zharfanw/fsaeuiicar/Gambar/messageImage_1562059117821.jpg

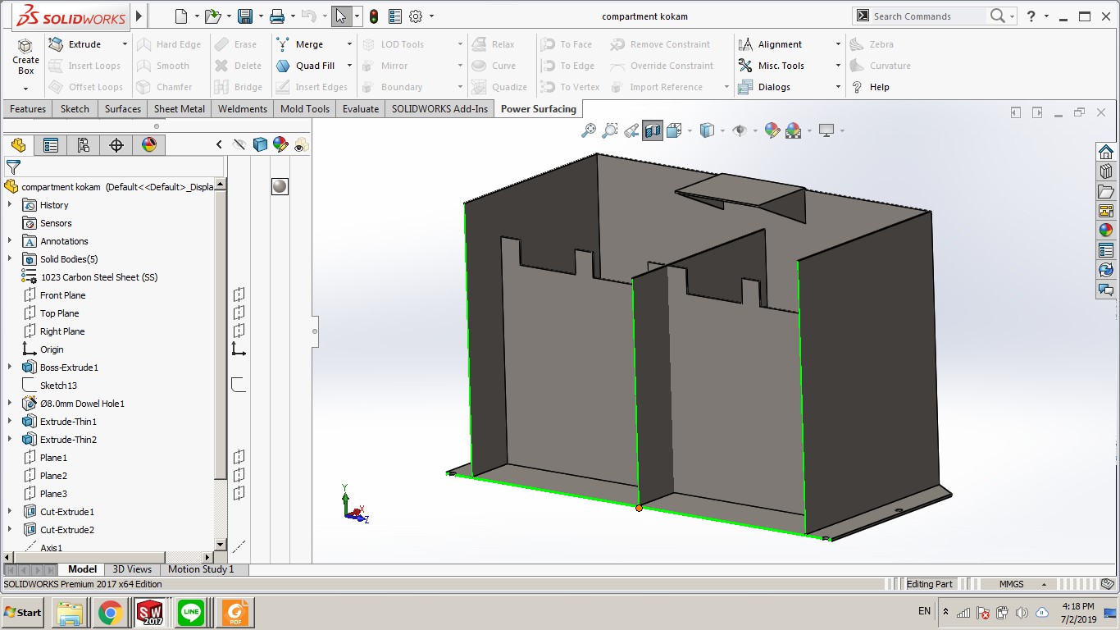
Gambar/messageImage_1562059117821.jpg
