zharfanw/fsaeuiicar/Rangkaian/DCDCCOnverter/DCDCConverter/DCDCConverter.sch

## KiCad design Rangkaian/DCDCCOnverter/DCDCConverter/DCDCConverter.sch (2019-09-29)

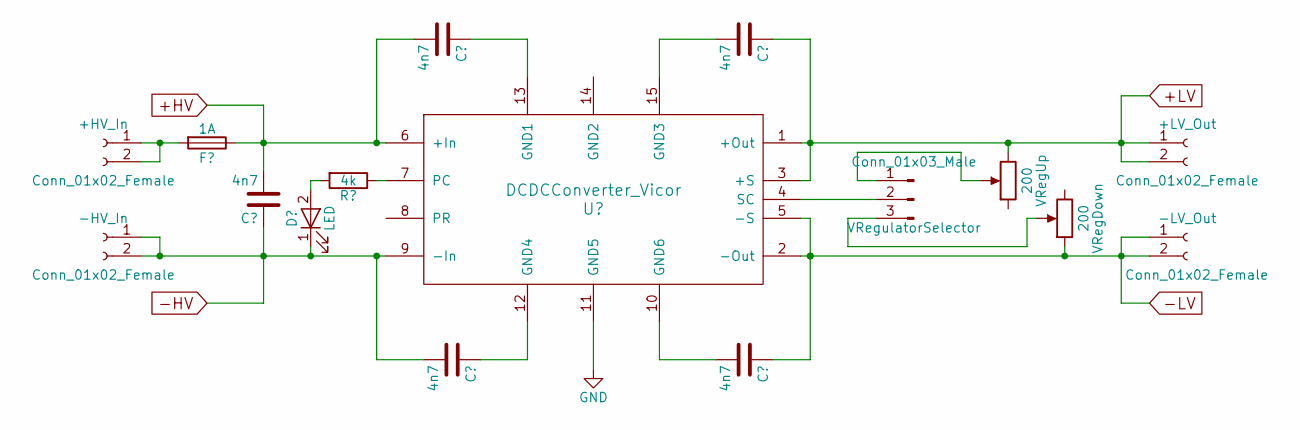
[picture p31: schematic DCDCConverter.sch]

Parts:
+HV_In: Conn_01x02_Female
+LV_Out: Conn_01x02_Female
-HV_In: Conn_01x02_Female
-LV_Out: Conn_01x02_Female
VRegDown: 200
VRegUp: 200
VRegulatorSelector: Conn_01x03_Male

Connections:
+LV: +LV_Out.1, +LV_Out.2, VRegUp.3
-HV: -HV_In.1, -HV_In.2
-LV: -LV_Out.1, -LV_Out.2, VRegDown.1
unnamed: +HV_In.1, +HV_In.2
unnamed: VRegDown.2, VRegulatorSelector.3
unnamed: VRegUp.2, VRegulatorSelector.1
